rosalyntg/donut/pwm.asc

C1: cap; 220p
D1: diode; 1N914
D2: diode; 1N914
R1: res; 500
R2: res; 100k
R3: res; 0
U1: NE555
V1: voltage; 5
Named nets: 0, 5V, OUT
.tran 1m
